Technariumas/smalsiukas/line-sensor/line-sensor-bottom.png

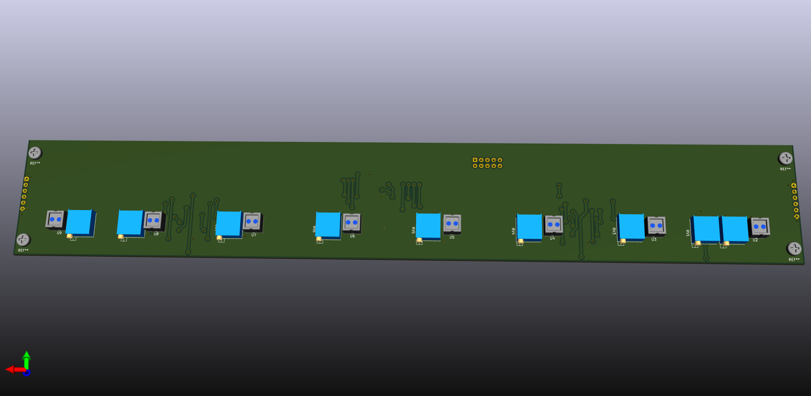
line-sensor/line-sensor-bottom.png
