Technariumas/smalsiukas/line-sensor/line-sensor-top.png

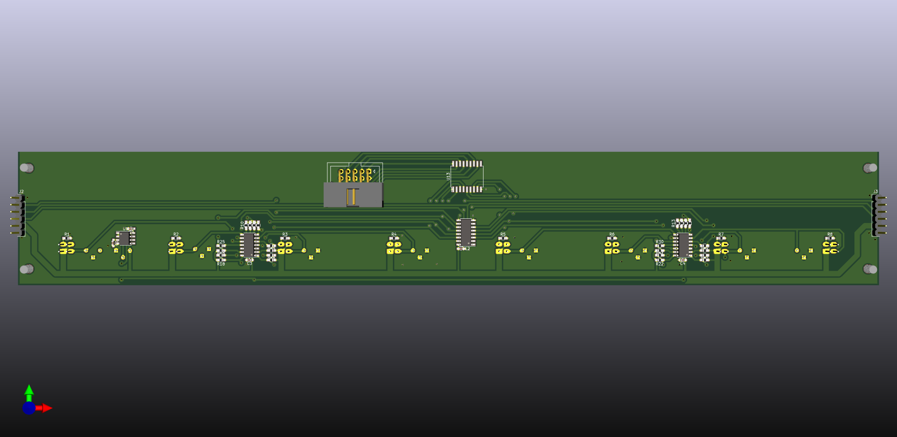
line-sensor/line-sensor-top.png
