Technariumas/smalsiukas/media/IMG_20170316_202355.jpg

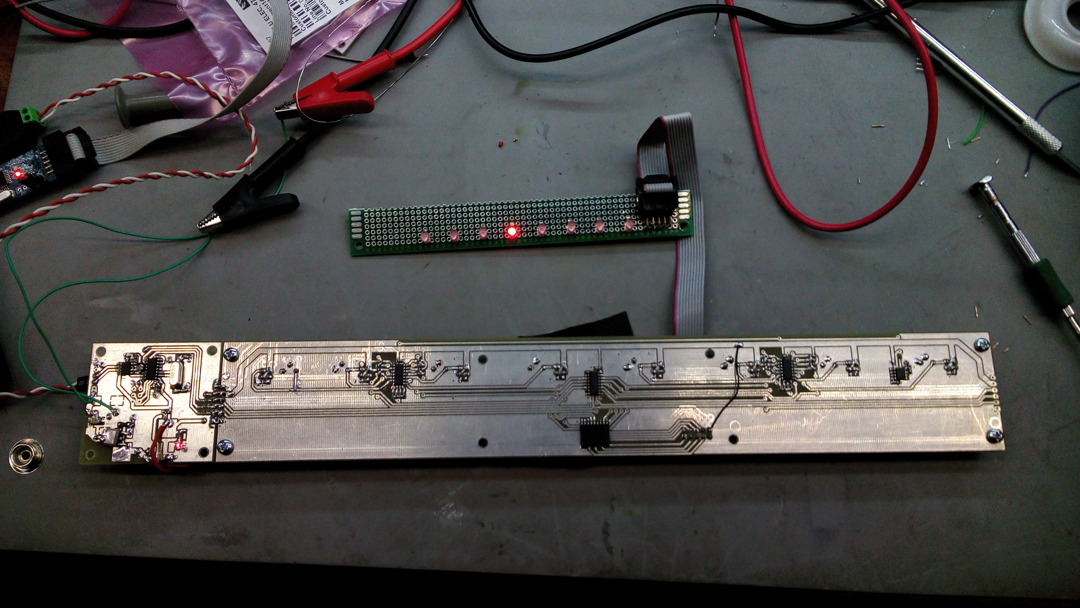
media/IMG_20170316_202355.jpg
