Technariumas/smalsiukas/media/IMG_20170401_115345.jpg

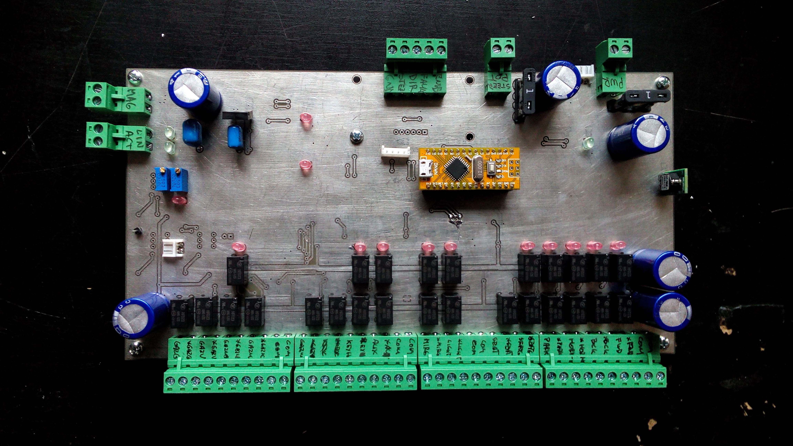
media/IMG_20170401_115345.jpg
