Technariumas/smalsiukas/media/IMG_20170401_115623.jpg

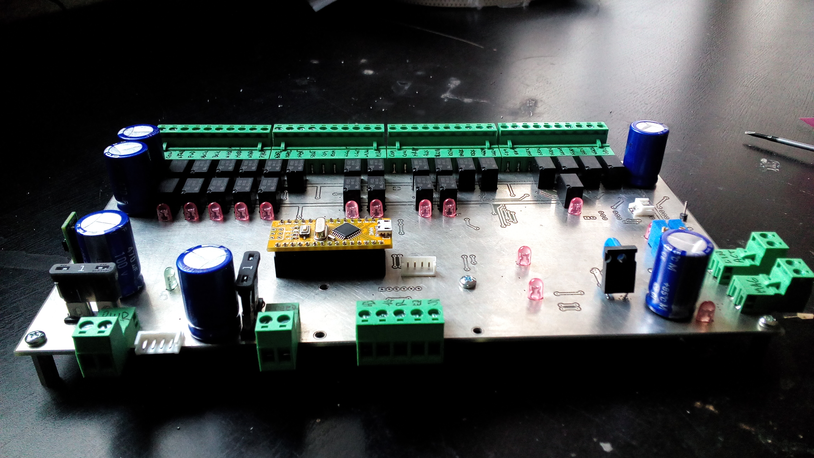
media/IMG_20170401_115623.jpg
