Technariumas/smalsiukas/media/IMG_20170402_200632.jpg

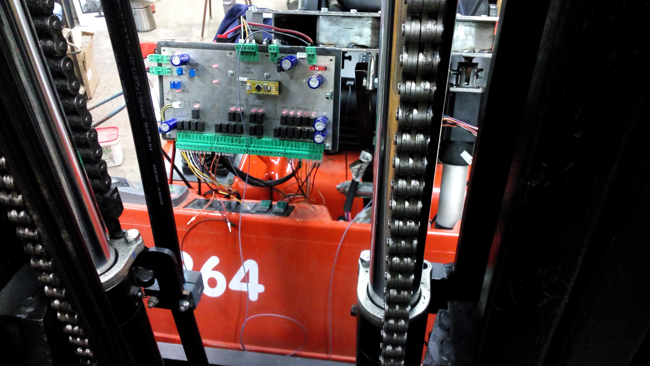
media/IMG_20170402_200632.jpg
