Technariumas/smalsiukas/media/IMG_20170402_200637.jpg

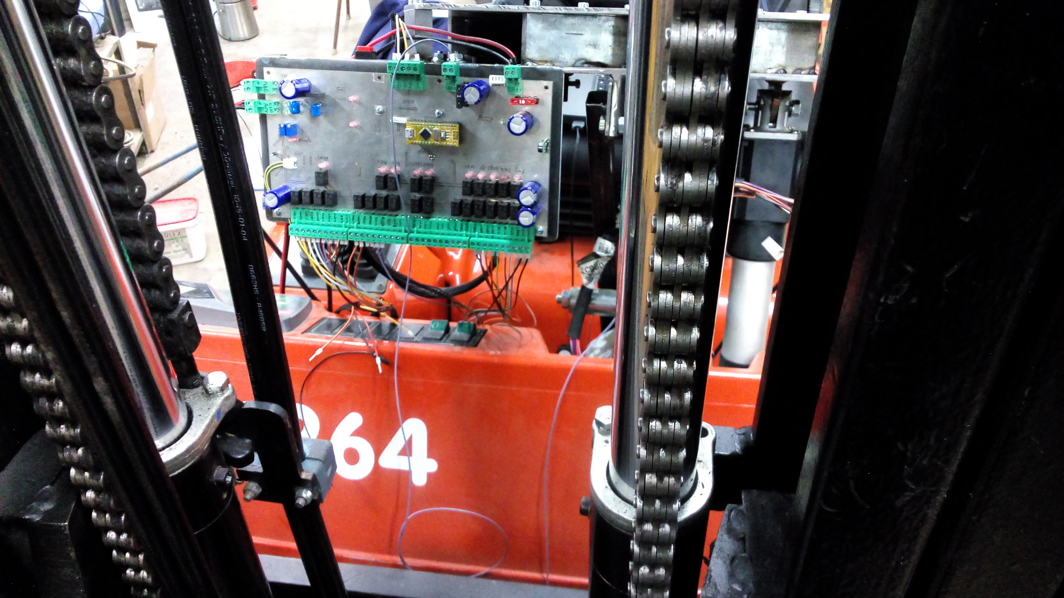
media/IMG_20170402_200637.jpg
