Technariumas/smalsiukas/Toyota/Mechanics/Blueprints/Toyota steering wheel holder blueprint.jpg

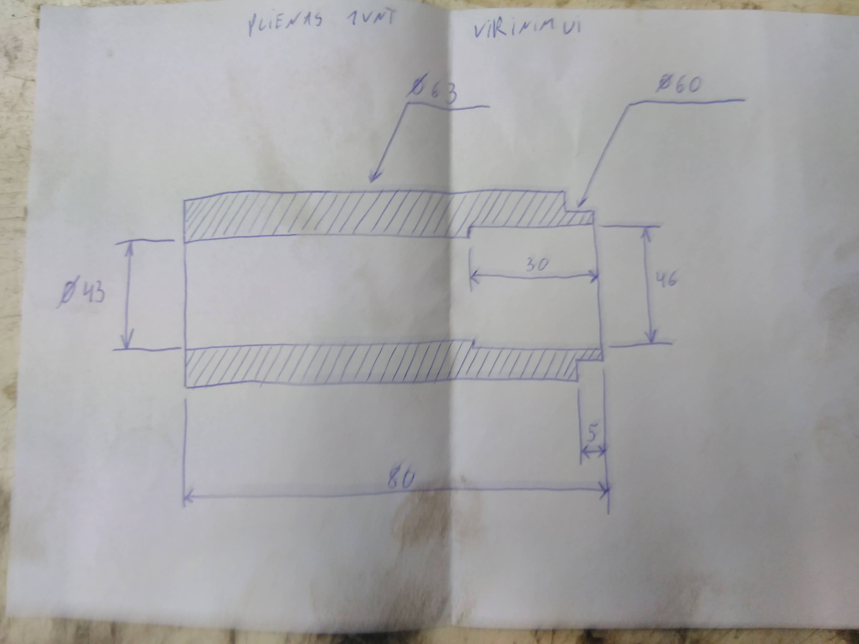
Toyota/Mechanics/Blueprints/Toyota steering wheel holder blueprint.jpg
