Technariumas/smalsiukas/Toyota/Mechanics/Blueprints/Toyota steering wheel hub blueprint1.jpg

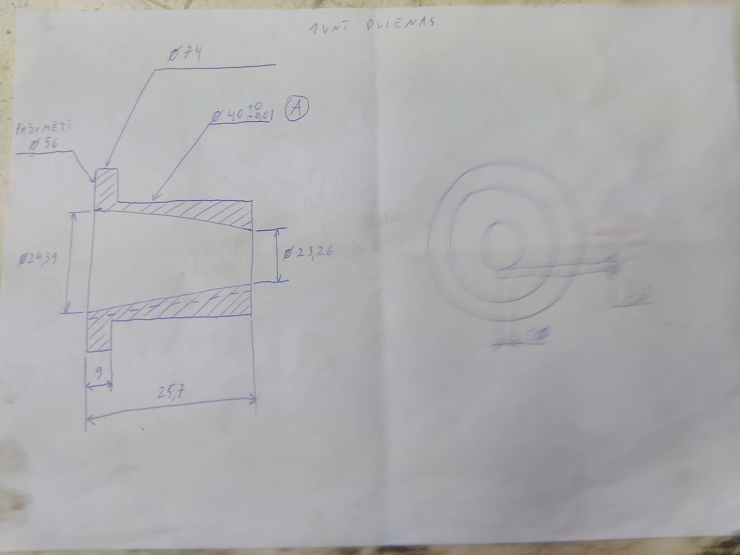
Toyota/Mechanics/Blueprints/Toyota steering wheel hub blueprint1.jpg
