Technariumas/smalsiukas/Toyota/Mechanics/Blueprints/Toyota steering wheel pulleys blueprint.jpg

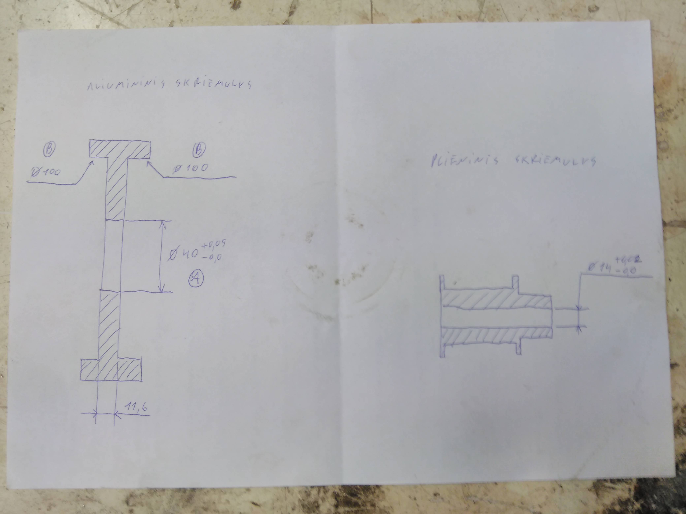
Toyota/Mechanics/Blueprints/Toyota steering wheel pulleys blueprint.jpg
