Technariumas/smalsiukas/LINDE/Mechanics/Parts/Steering wheel/Linde steering wheel1.jpg

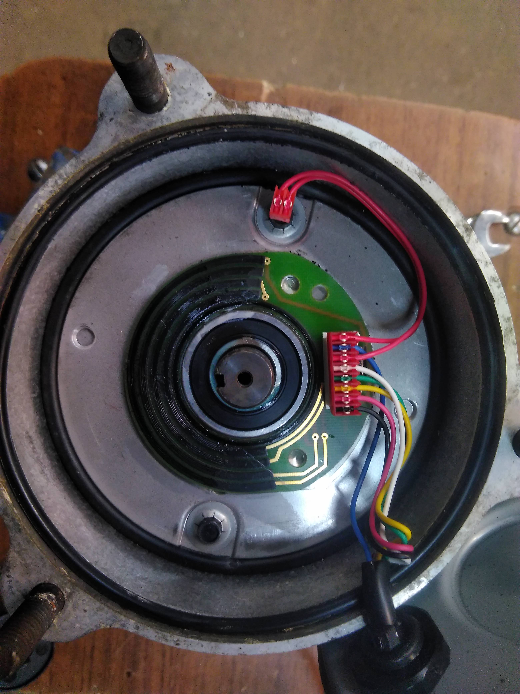
LINDE/Mechanics/Parts/Steering wheel/Linde steering wheel1.jpg
