Technariumas/smalsiukas/LINDE/Mechanics/Parts/Steering wheel/Linde steering wheel2.jpg

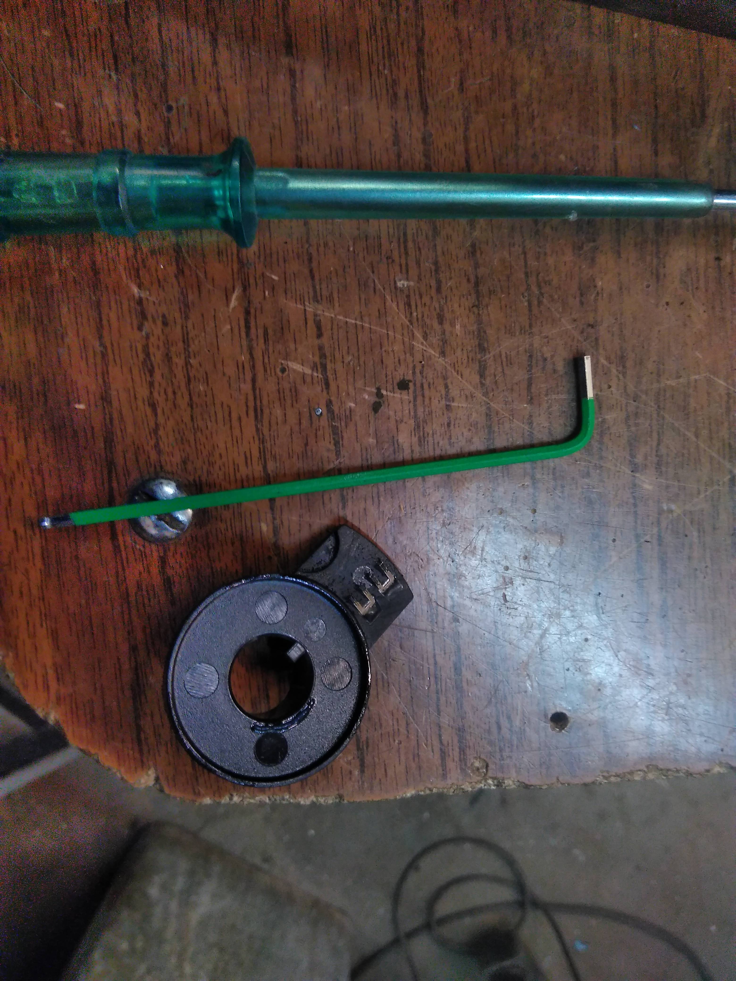
LINDE/Mechanics/Parts/Steering wheel/Linde steering wheel2.jpg
