Technariumas/smalsiukas/LINDE/Mechanics/Parts/Steering wheel/Linde steering wheel3.jpg

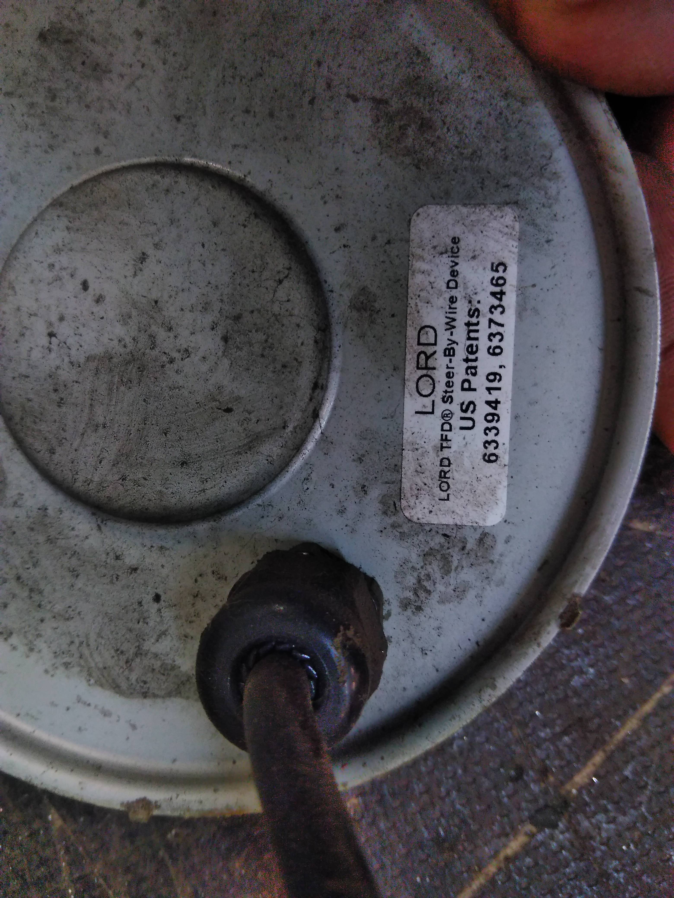
LINDE/Mechanics/Parts/Steering wheel/Linde steering wheel3.jpg
