Technariumas/smalsiukas/LINDE/Mechanics/Parts/Steering wheel/Linde steering wheel.jpg

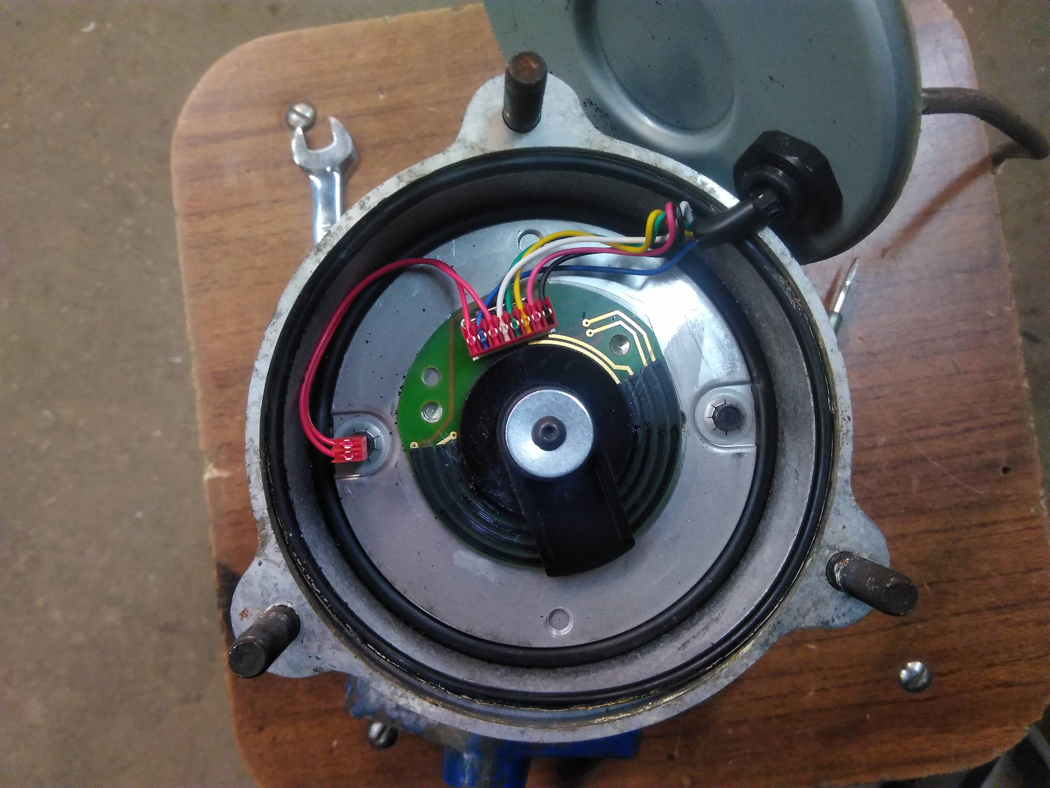
LINDE/Mechanics/Parts/Steering wheel/Linde steering wheel.jpg
