Technariumas/smalsiukas/Toyota/Mechanics/Blueprints/Toyota steering wheel parts blueprint.jpg

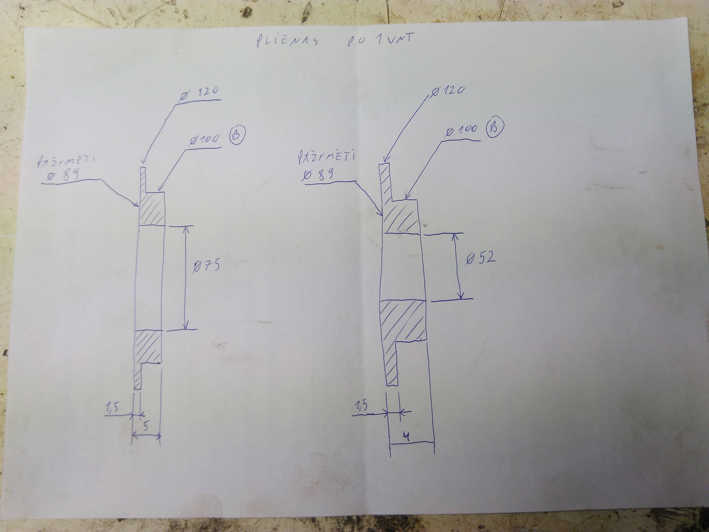
Toyota/Mechanics/Blueprints/Toyota steering wheel parts blueprint.jpg
