Technariumas/smalsiukas/Toyota/Mechanics/Parts/Emergency brake/Toyota emergency brake actuator.jpg

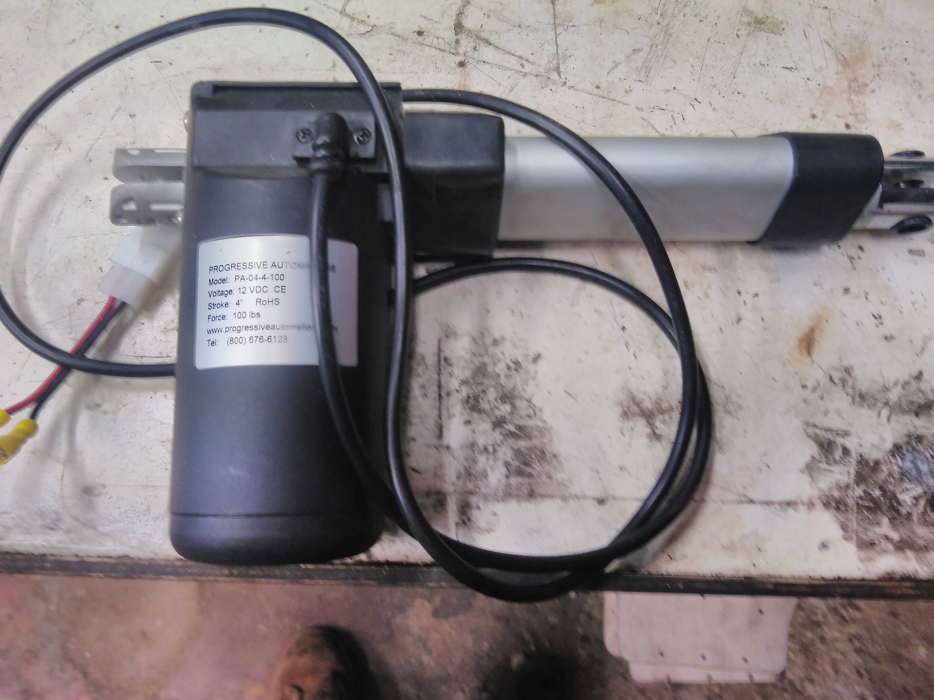
Toyota/Mechanics/Parts/Emergency brake/Toyota emergency brake actuator.jpg
