Technariumas/smalsiukas/Toyota/Mechanics/Parts/Emergency brake/Toyota emergency brake magnet.jpg

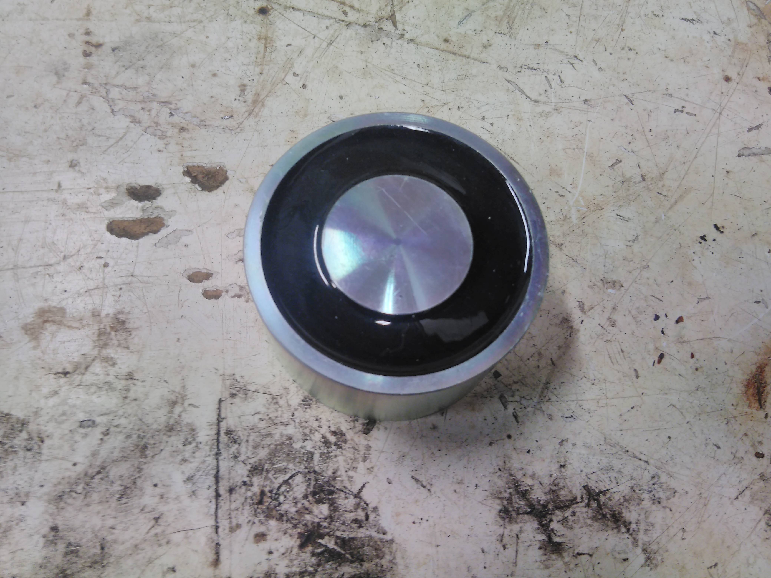
Toyota/Mechanics/Parts/Emergency brake/Toyota emergency brake magnet.jpg
