Technariumas/smalsiukas/Toyota/Mechanics/Parts/random/Getting in2.jpg

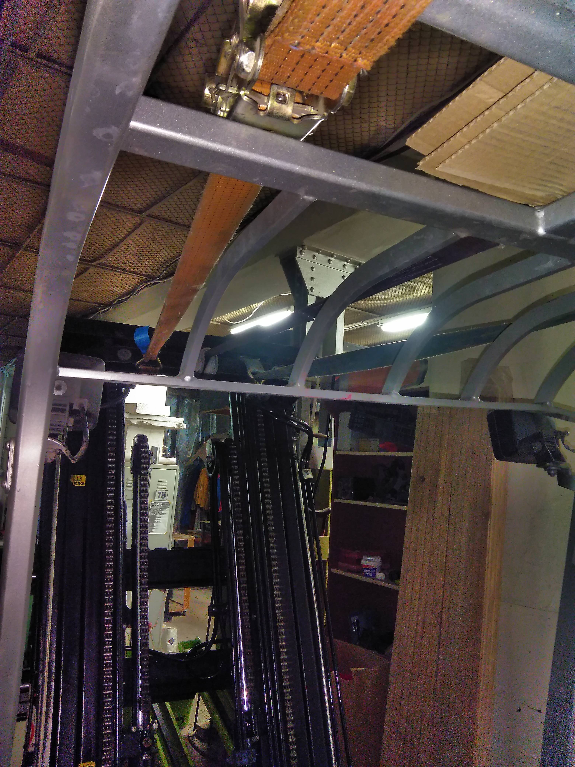
Toyota/Mechanics/Parts/random/Getting in2.jpg
