Technariumas/smalsiukas/Toyota/Mechanics/Parts/random/Getting in.jpg

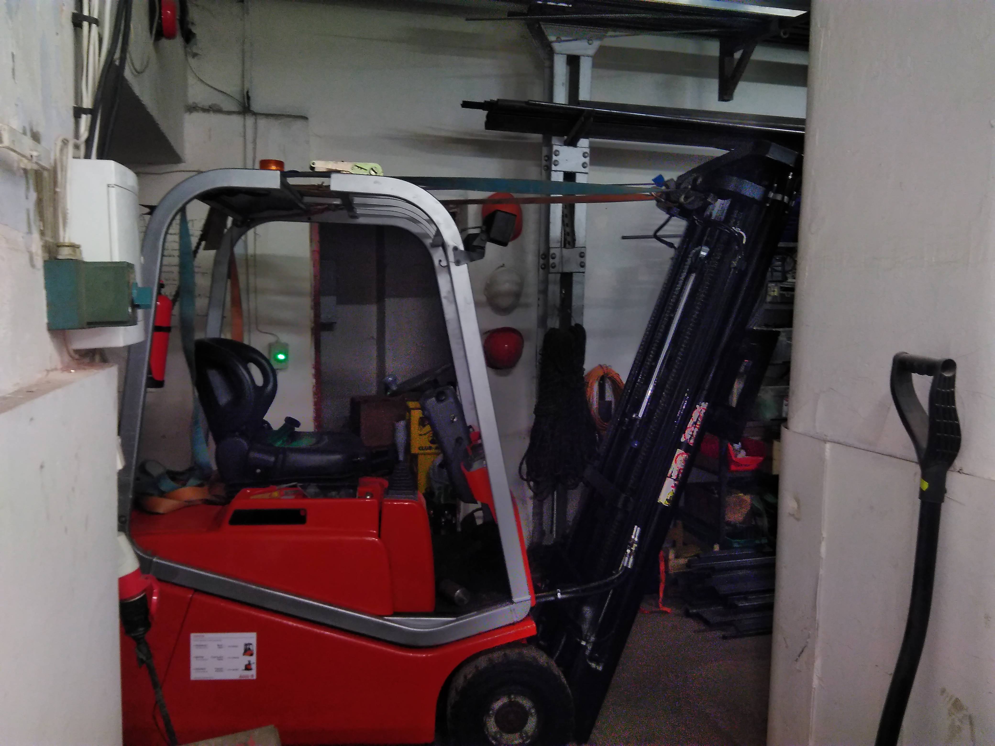
Toyota/Mechanics/Parts/random/Getting in.jpg
