Technariumas/smalsiukas/Toyota/Mechanics/Parts/steering wheel/Stepper driver.jpg

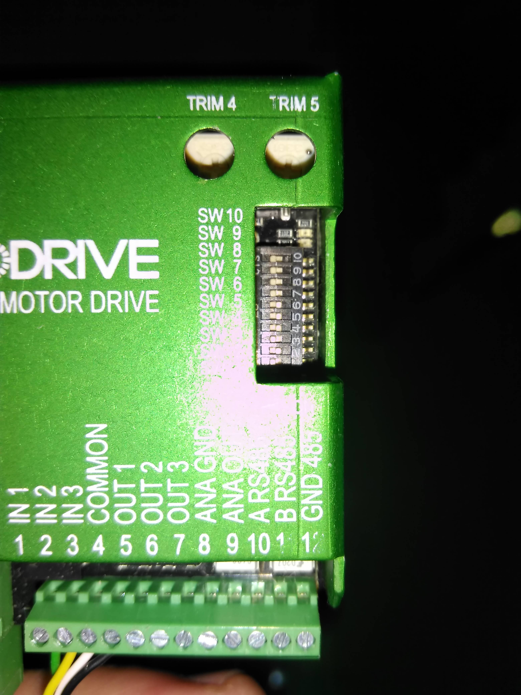
Toyota/Mechanics/Parts/steering wheel/Stepper driver.jpg
