Technariumas/smalsiukas/Toyota/Mechanics/Parts/steering wheel/Toyota steering wheel attachment1.jpg

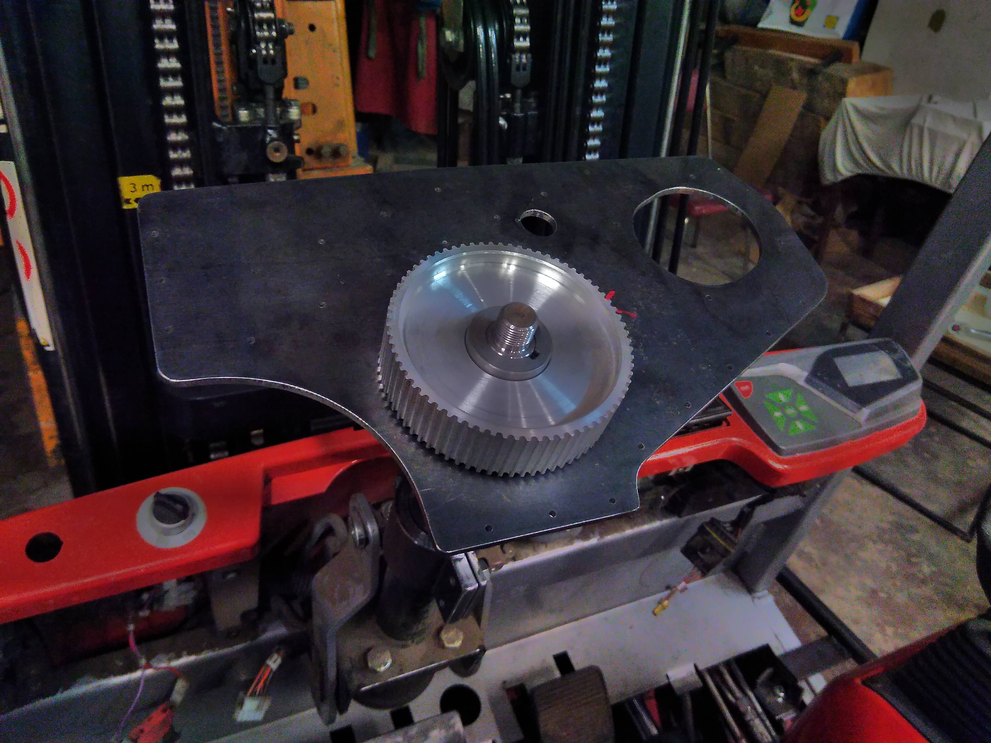
Toyota/Mechanics/Parts/steering wheel/Toyota steering wheel attachment1.jpg
