Technariumas/smalsiukas/Toyota/Mechanics/Parts/steering wheel/Toyota steering wheel attachment2.jpg

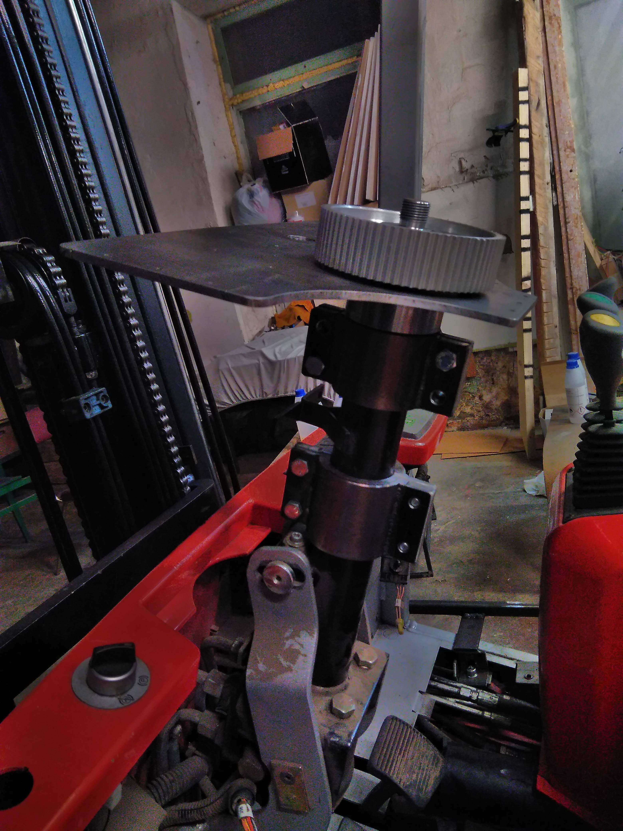
Toyota/Mechanics/Parts/steering wheel/Toyota steering wheel attachment2.jpg
