Technariumas/smalsiukas/Toyota/Mechanics/Parts/steering wheel/Toyota steering wheel holder1.jpg

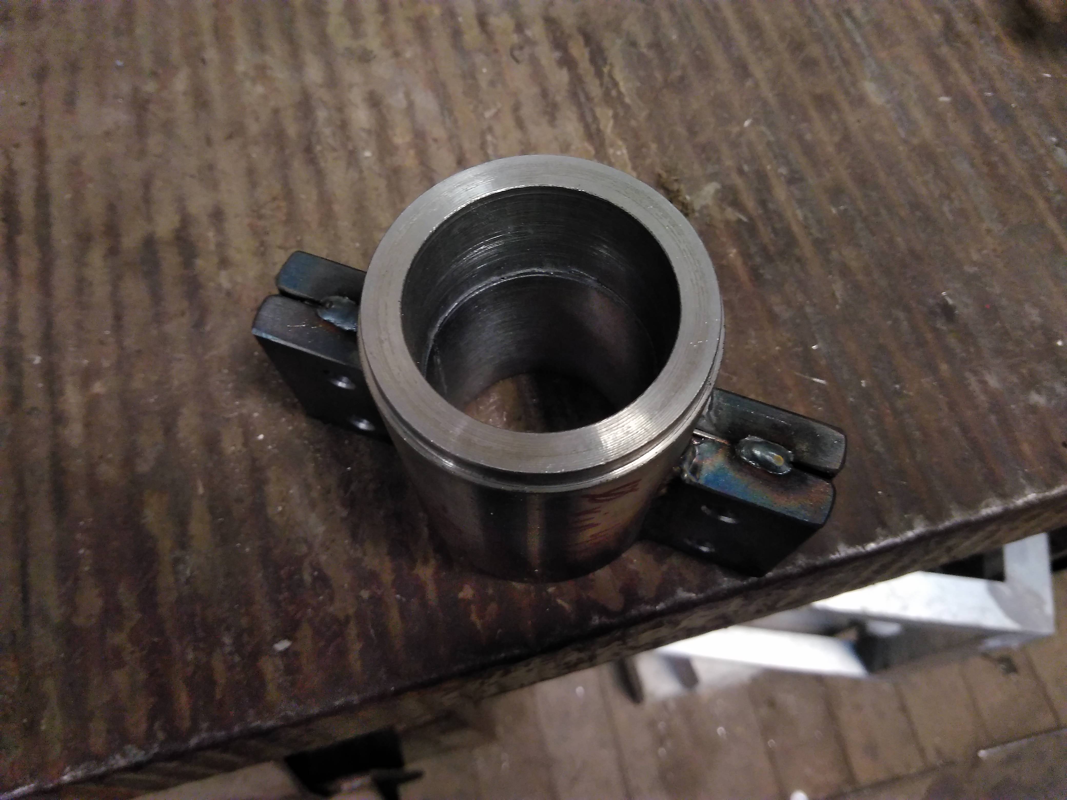
Toyota/Mechanics/Parts/steering wheel/Toyota steering wheel holder1.jpg
