Technariumas/smalsiukas/Toyota/Mechanics/Parts/steering wheel/Toyota steering wheel holder2.jpg

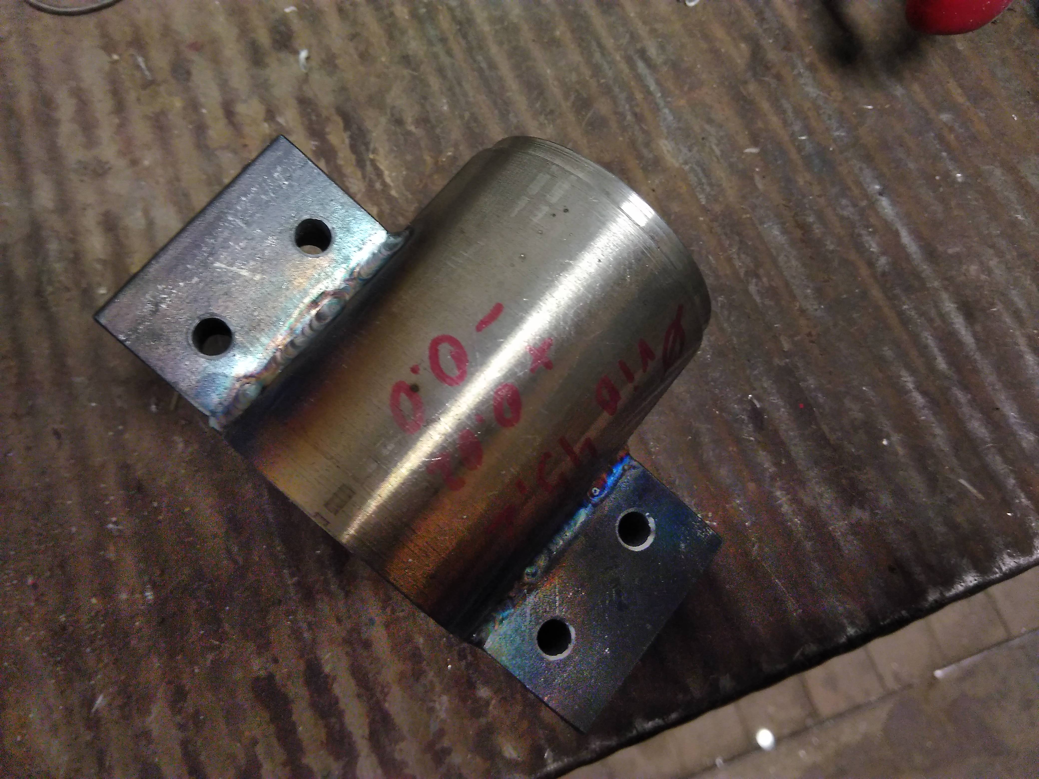
Toyota/Mechanics/Parts/steering wheel/Toyota steering wheel holder2.jpg
