Technariumas/smalsiukas/Toyota/Mechanics/Parts/steering wheel/Toyota steering wheel holder3.jpg

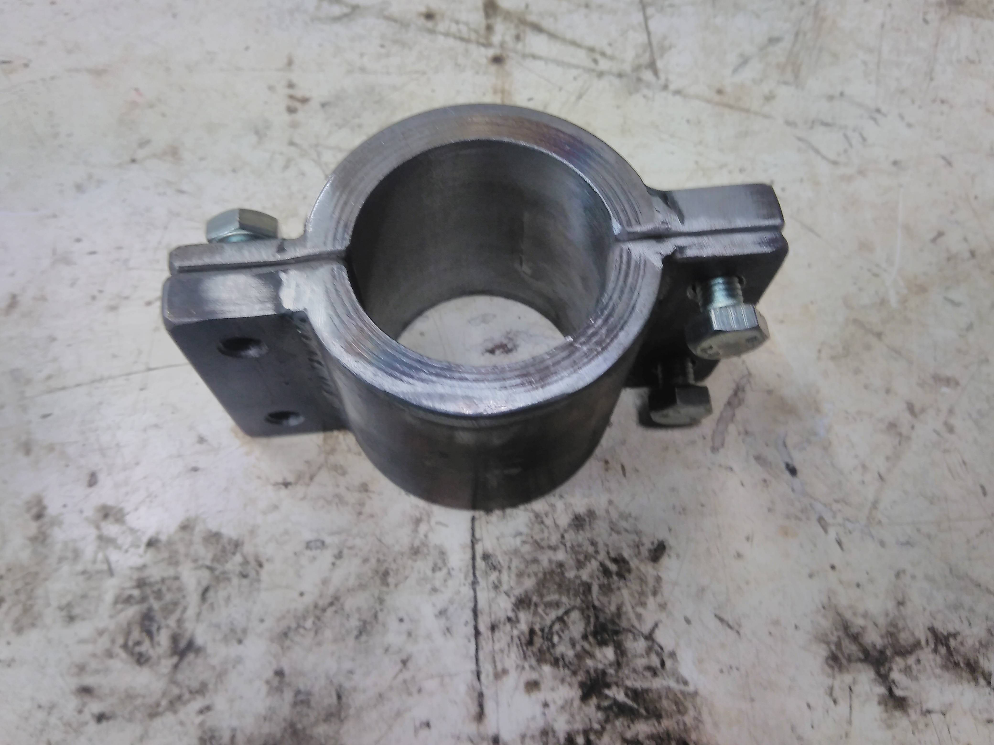
Toyota/Mechanics/Parts/steering wheel/Toyota steering wheel holder3.jpg
