Technariumas/smalsiukas/Toyota/Mechanics/Parts/steering wheel/Toyota steering wheel holder.jpg

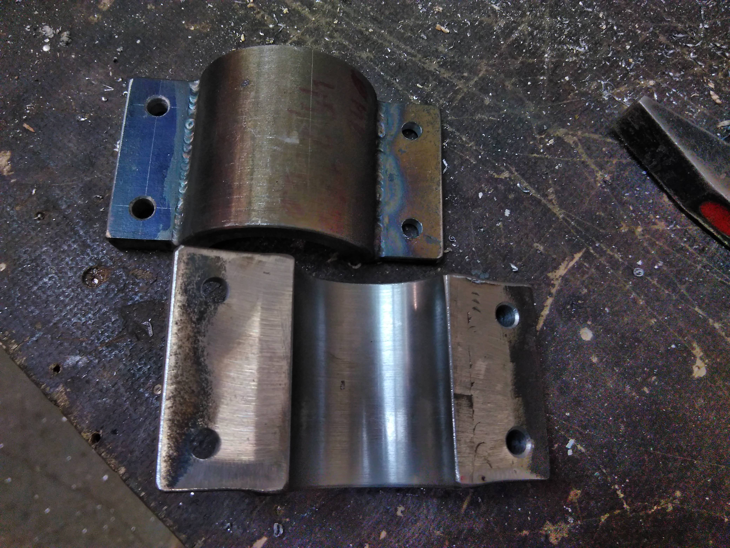
Toyota/Mechanics/Parts/steering wheel/Toyota steering wheel holder.jpg
