Technariumas/smalsiukas/Toyota/Mechanics/Parts/steering wheel/Toyota steering wheel hub.jpg

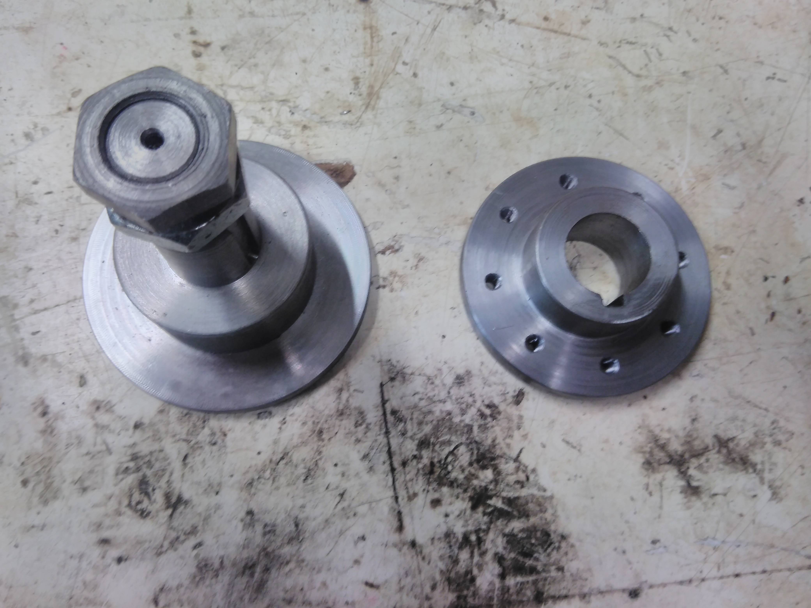
Toyota/Mechanics/Parts/steering wheel/Toyota steering wheel hub.jpg
