Technariumas/smalsiukas/Toyota/Mechanics/Parts/steering wheel/Toyota steering wheel plate1.jpg

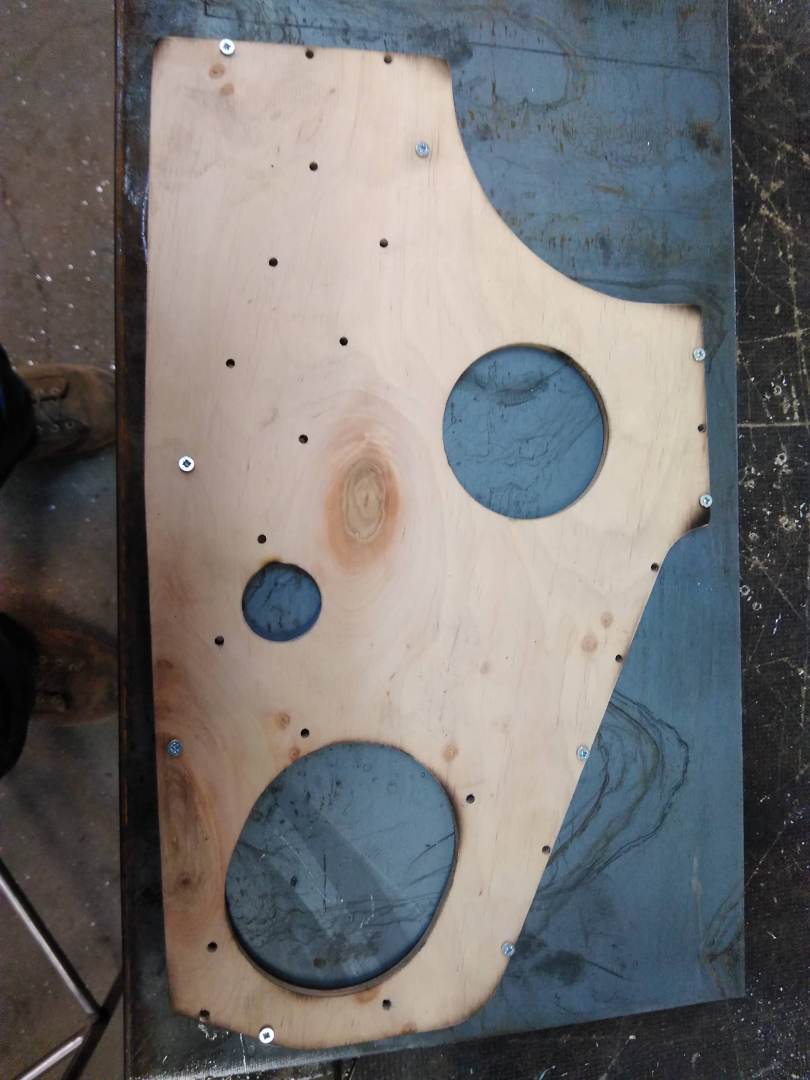
Toyota/Mechanics/Parts/steering wheel/Toyota steering wheel plate1.jpg
