Technariumas/smalsiukas/Toyota/Mechanics/Parts/steering wheel/Toyota steering wheel plate2.jpg

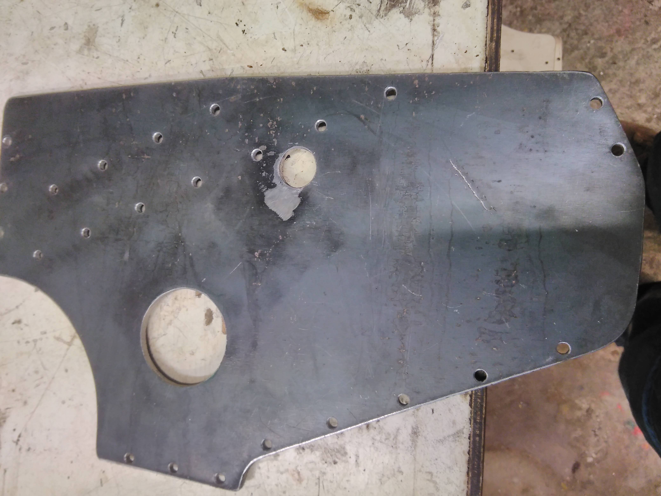
Toyota/Mechanics/Parts/steering wheel/Toyota steering wheel plate2.jpg
