Technariumas/smalsiukas/Toyota/Mechanics/Parts/steering wheel/Toyota steering wheel plate3.jpg

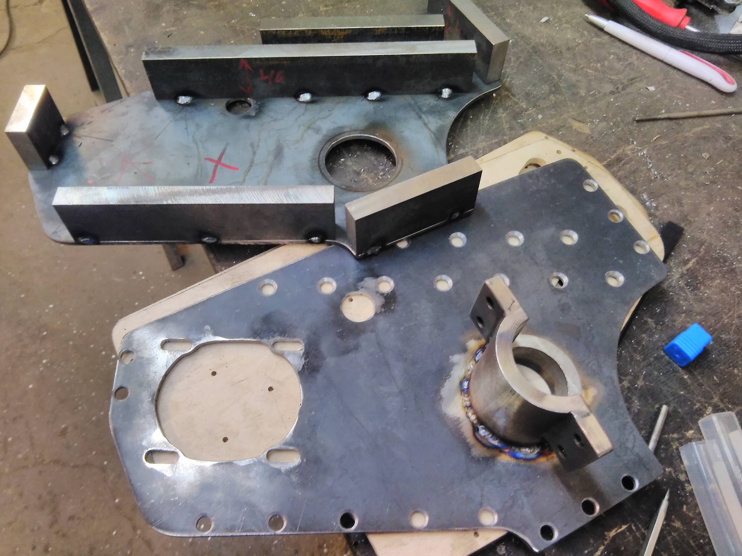
Toyota/Mechanics/Parts/steering wheel/Toyota steering wheel plate3.jpg
