Technariumas/smalsiukas/Toyota/Mechanics/Parts/steering wheel/Toyota steering wheel plate4.jpg

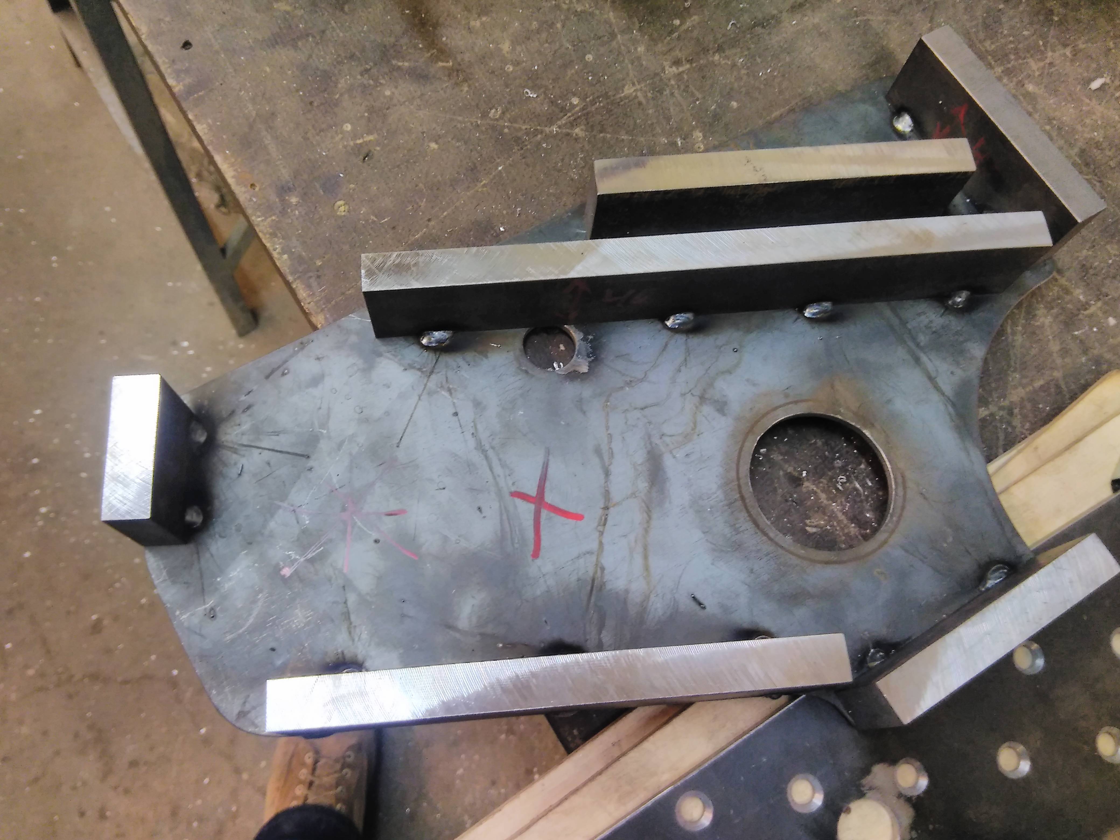
Toyota/Mechanics/Parts/steering wheel/Toyota steering wheel plate4.jpg
