Technariumas/smalsiukas/Toyota/Mechanics/Parts/steering wheel/Toyota steering wheel plate5.jpg

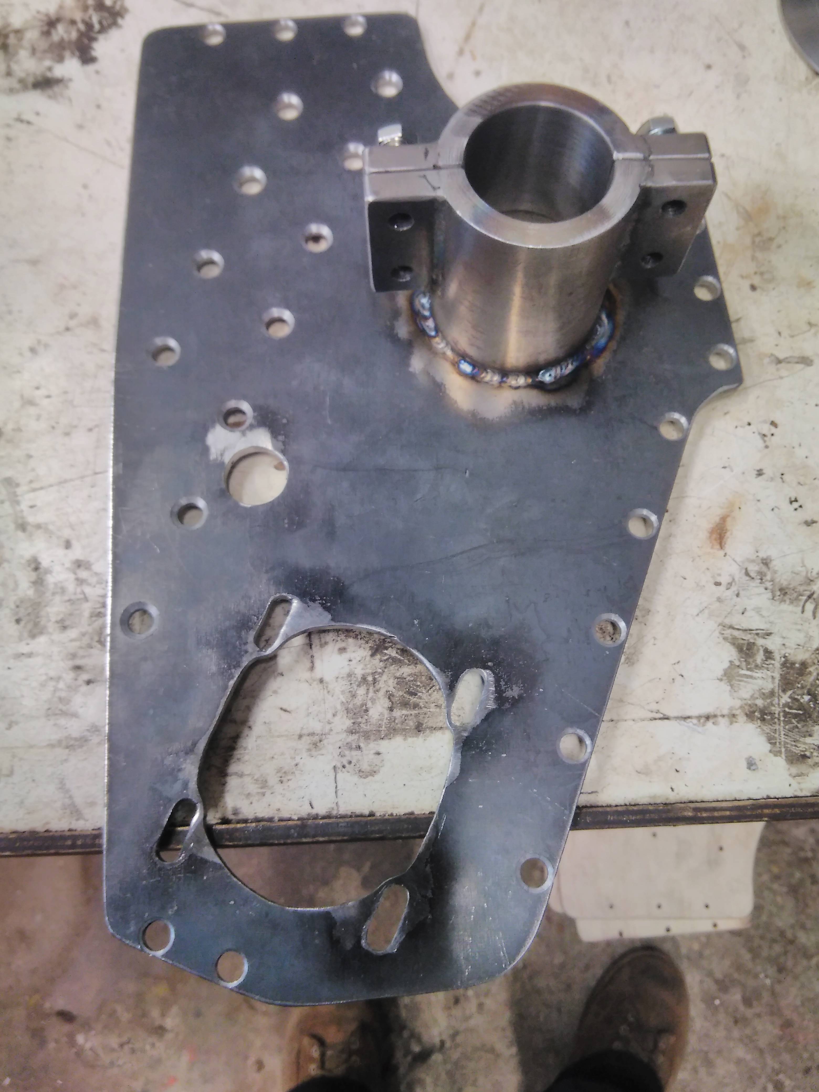
Toyota/Mechanics/Parts/steering wheel/Toyota steering wheel plate5.jpg
