Technariumas/smalsiukas/Toyota/Mechanics/Parts/steering wheel/Toyota steering wheel plate6.jpg

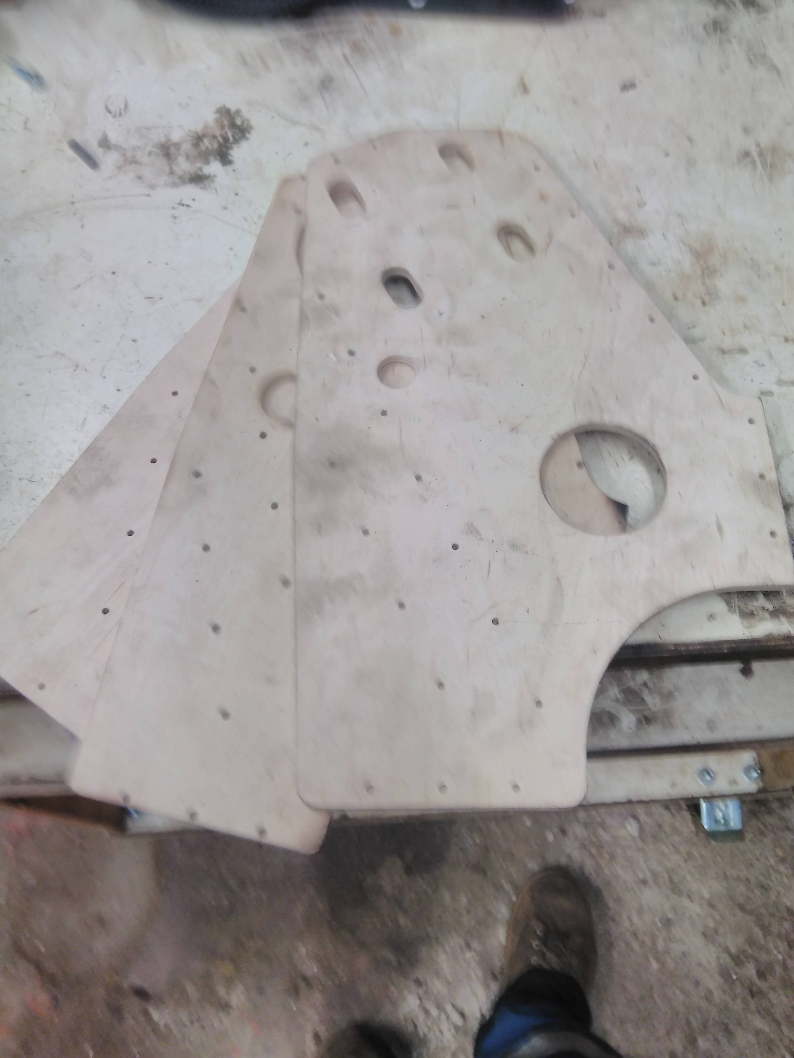
Toyota/Mechanics/Parts/steering wheel/Toyota steering wheel plate6.jpg
