Technariumas/smalsiukas/Toyota/Mechanics/Parts/steering wheel/Toyota steering wheel pulleys.jpg

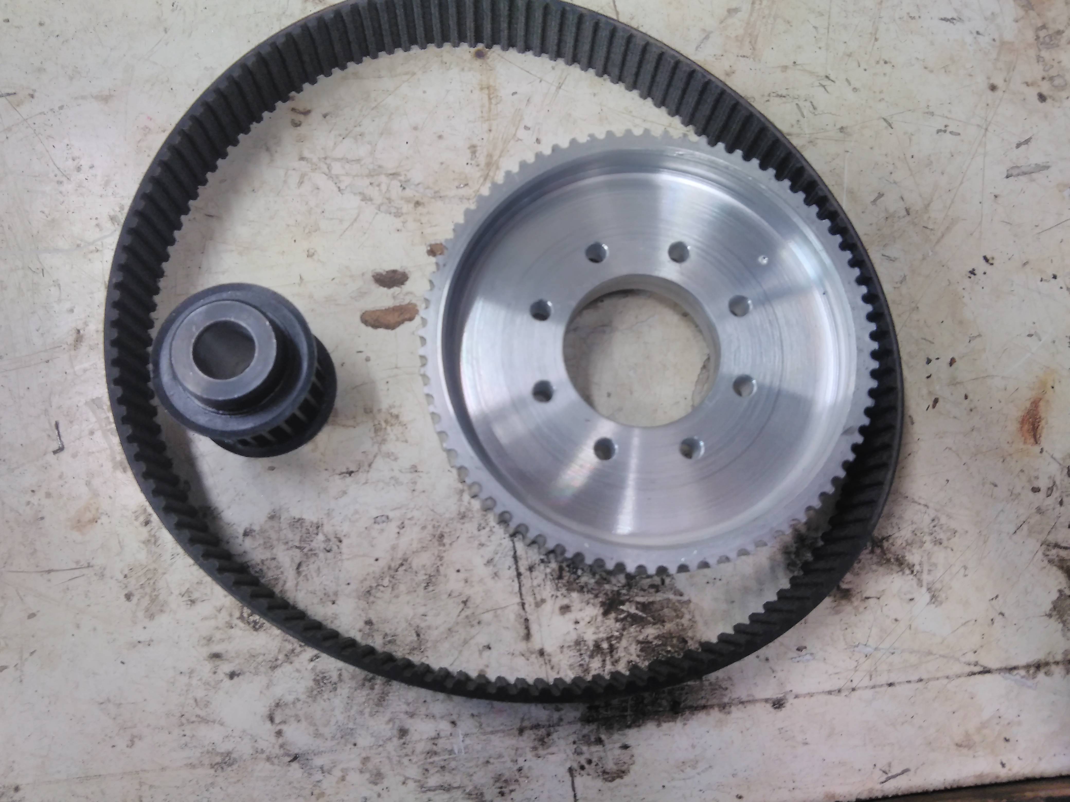
Toyota/Mechanics/Parts/steering wheel/Toyota steering wheel pulleys.jpg
