Technariumas/smalsiukas/Toyota/Mechanics/Parts/steering wheel/Toyota steering wheel stepper.jpg

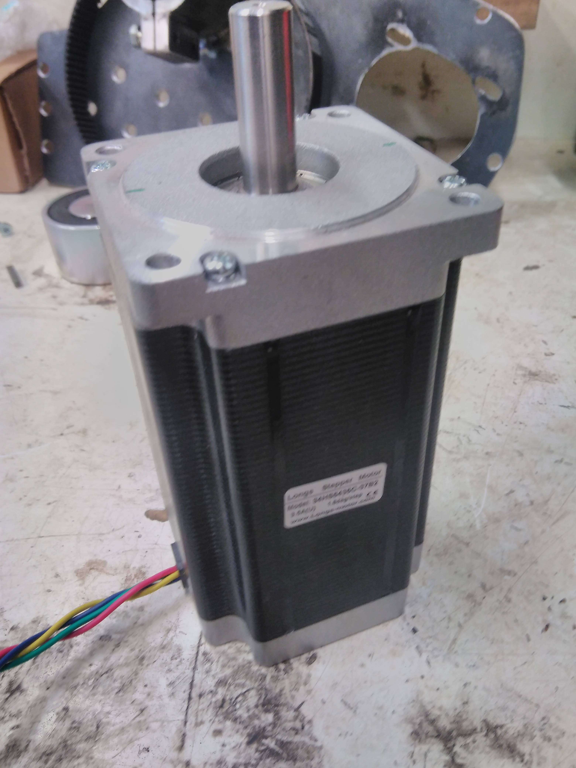
Toyota/Mechanics/Parts/steering wheel/Toyota steering wheel stepper.jpg
