Technariumas/smalsiukas/lindukas/control.h

#ifndef __CONTROL_H
#define __CONTROL_H
#include "Arduino.h"
#include "pins.h"
void gazOff(void);
void gazOn(void);

void controlTakeover() {
	digitalWrite(TAKEOVER, HIGH);
}

void controlRelease() {
	digitalWrite(TAKEOVER, LOW);
}

void keyOn() {
}

void keyOff() {
}



uint8_t control = 0;

#define CTRL_SEAT 		0b00000001
#define CTRL_PARKING	0b00000010
#define CTRL_HORN		0b00000100
#define CTRL_DIR_BACK	0b00001000
#define CTRL_DIR_FWD	0b00010000
#define CTRL_GAZ		0b00100000
#define CTRL_MIRGALKE	0b01000000
#define CTRL_LIGHTS		0b10000000

#define LED_STAGE_1  0b00001000
#define LED_STAGE_2  0b00010000
#define LED_STAGE_3     0b00000001
#define LED_STAGE_4  0b00000010

void sendControl() {
	digitalWrite(SPI_LATCH, LOW);
 	shiftOut(SPI_DATA, SPI_CLK, MSBFIRST, control);  
	digitalWrite(SPI_LATCH, HIGH);
}

void seatEnable() {
	control = control | CTRL_SEAT;
	sendControl();
}

void seatDisable() {
	control = control & ~CTRL_SEAT;
	sendControl();
}

void parkingOn() {
	control = control & ~CTRL_PARKING;
	sendControl();
}

void parkingOff() {
	control = control | CTRL_PARKING;
	sendControl();
}

void hornOn() {
	control = control | CTRL_HORN;
	sendControl();
}

void hornOff() {
	control = control & ~CTRL_HORN;
	sendControl();
}

void directionForwardOn() {
	control = control | CTRL_DIR_FWD;
	control = control & ~CTRL_DIR_BACK;
	sendControl();
}

void directionBackwardOn() {
	control = control | CTRL_DIR_BACK;
	control = control & ~CTRL_DIR_FWD;
	sendControl();
}

void directionOff() {
	control = control & ~CTRL_DIR_FWD;
	control = control & ~CTRL_DIR_BACK;
	sendControl();
}

void lightsOn() {
	control = control | CTRL_LIGHTS;
	sendControl();
}

void lightsOff() {
	control = control & ~CTRL_LIGHTS;
	sendControl();
}

void mirgalkeOn() {
	control = control | CTRL_MIRGALKE;
	sendControl();
}

void mirgalkeOff() {
	control = control & ~CTRL_MIRGALKE;
	sendControl();
}

void gazOn() {
	control = control | CTRL_GAZ;
	sendControl();
}

void gazOff() {
	control = control & ~CTRL_GAZ;
	sendControl();
}

void controlAllOff() {
	parkingOn();

	gazOff();
	mirgalkeOff();
	hornOff();
	lightsOff();
	directionOff();
	seatDisable();

	//gasDisable();
	//setSpeed(SPEED0);
	keyOff();
}

#endif
